DiyunZ/printer-energy-monitor-wiring/connector_detail.png

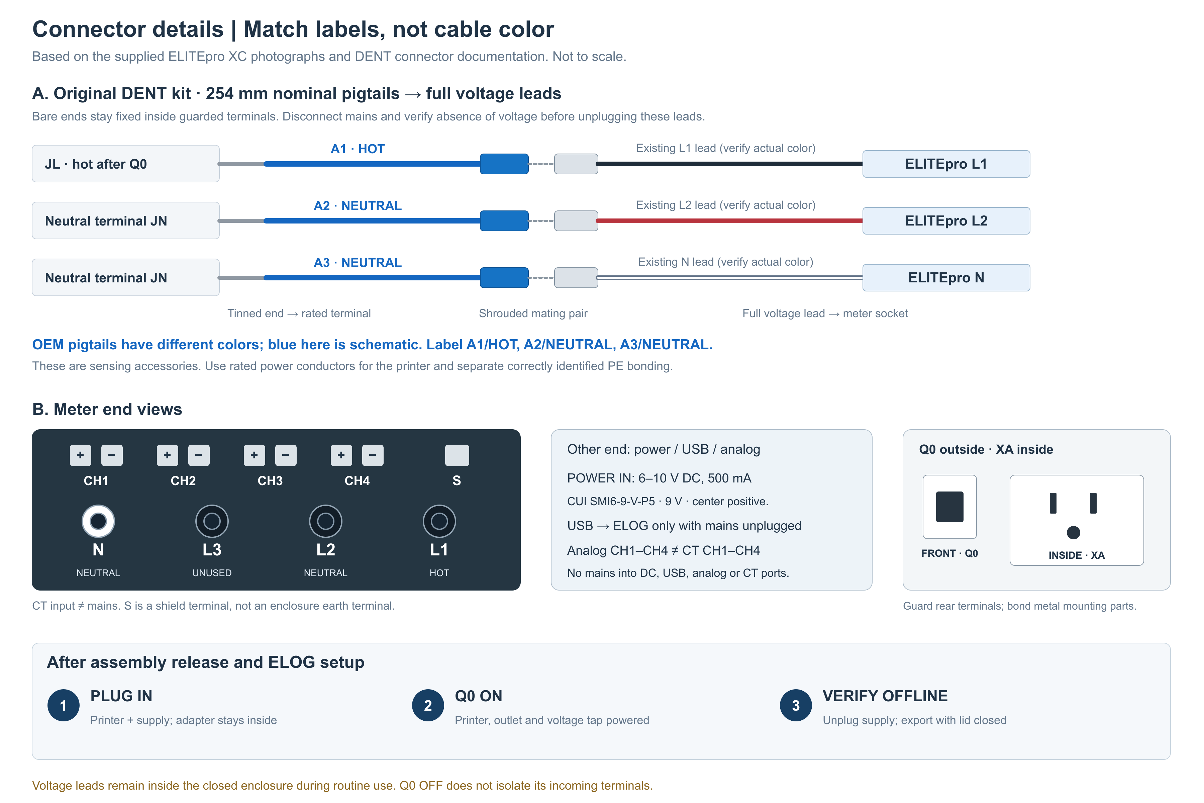
connector_detail.png
