DiyunZ/printer-energy-monitor-wiring/assets/materials/breaker.jpg

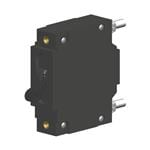
assets/materials/breaker.jpg
