DiyunZ/printer-energy-monitor-wiring/assets/materials/cord-glands.jpg

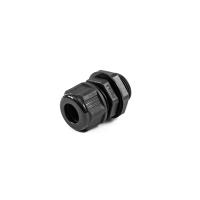
assets/materials/cord-glands.jpg
