DiyunZ/printer-energy-monitor-wiring/assets/materials/enclosure-nbf32126.jpg

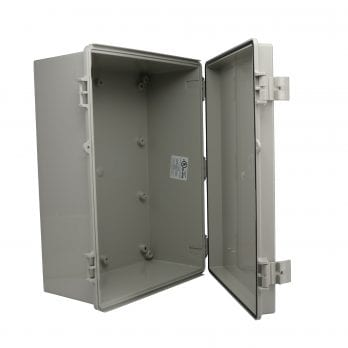
assets/materials/enclosure-nbf32126.jpg
