DiyunZ/printer-energy-monitor-wiring/assets/materials/fasteners-photo.jpg

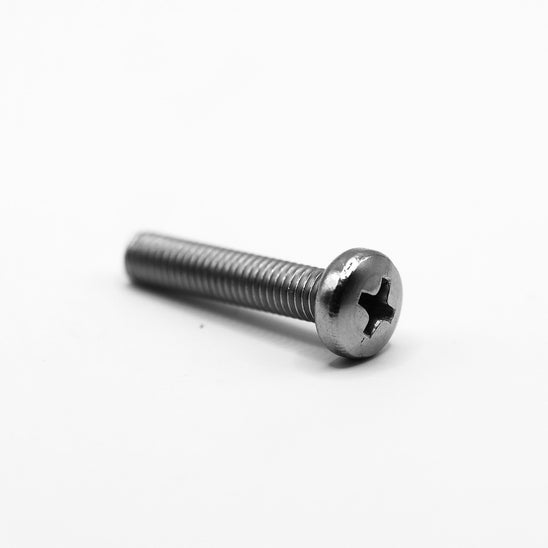
assets/materials/fasteners-photo.jpg
