DiyunZ/printer-energy-monitor-wiring/assets/materials/request-36-4703-ND.jpg

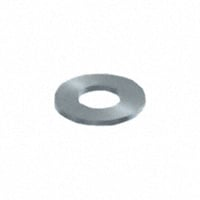
assets/materials/request-36-4703-ND.jpg
