DiyunZ/printer-energy-monitor-wiring/assets/materials/request-36-4705-ND.jpg

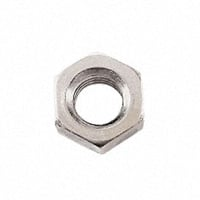
assets/materials/request-36-4705-ND.jpg
