DiyunZ/printer-energy-monitor-wiring/assets/materials/request-36-9911-ND.jpg

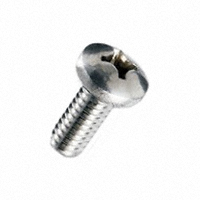
assets/materials/request-36-9911-ND.jpg
