DiyunZ/printer-energy-monitor-wiring/assets/materials/request-277-11849-ND.jpg

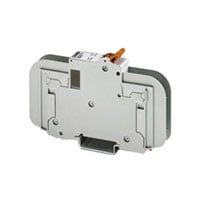
assets/materials/request-277-11849-ND.jpg
