DiyunZ/printer-energy-monitor-wiring/assets/materials/request-298-1030-ND.jpg

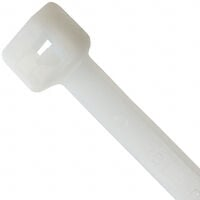
assets/materials/request-298-1030-ND.jpg
