DiyunZ/printer-energy-monitor-wiring/assets/materials/request-298-10245-ND.jpg

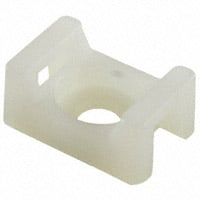
assets/materials/request-298-10245-ND.jpg
