DiyunZ/printer-energy-monitor-wiring/assets/materials/request-3720-3104-ND.jpg

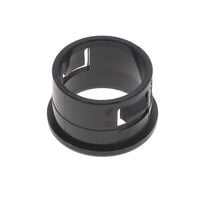
assets/materials/request-3720-3104-ND.jpg
