DiyunZ/printer-energy-monitor-wiring/assets/materials/request-204801237.jpg

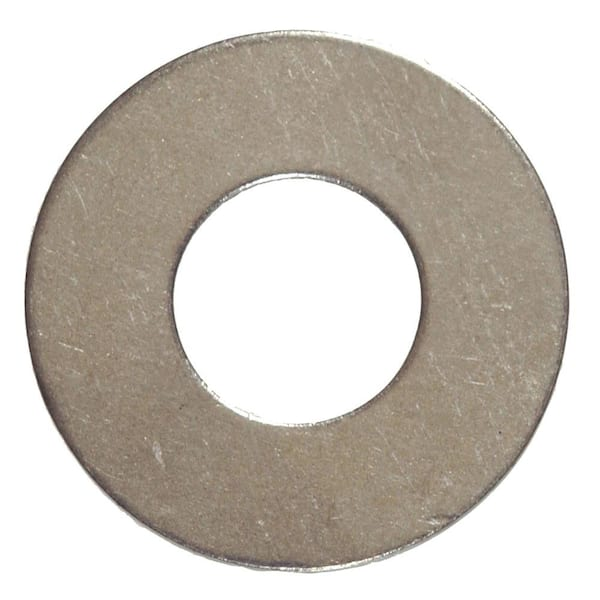
assets/materials/request-204801237.jpg
