DiyunZ/printer-energy-monitor-wiring/assets/materials/request-301304939.jpg

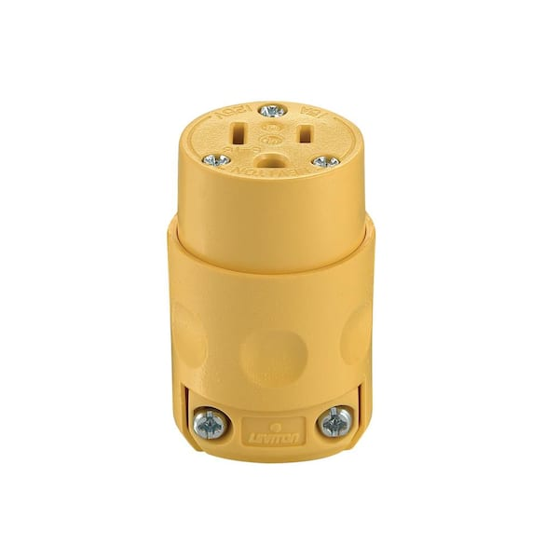
assets/materials/request-301304939.jpg
