DiyunZ/printer-energy-monitor-wiring/assets/materials/request-309610976.jpg

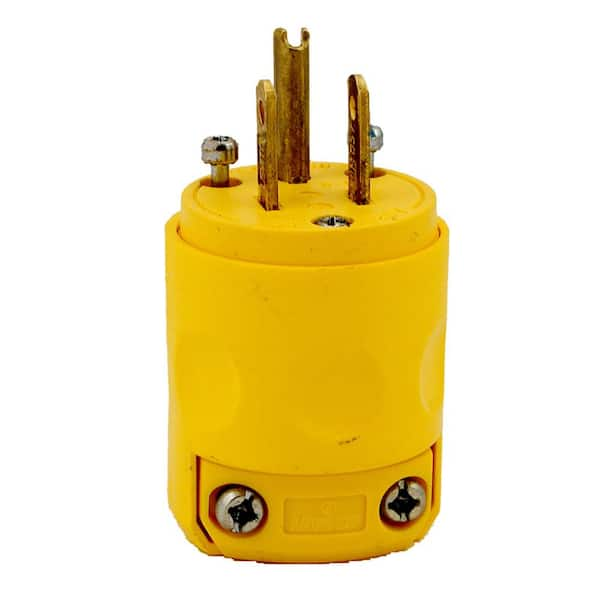
assets/materials/request-309610976.jpg
