DiyunZ/printer-energy-monitor-wiring/assets/materials/request-317479556.jpg

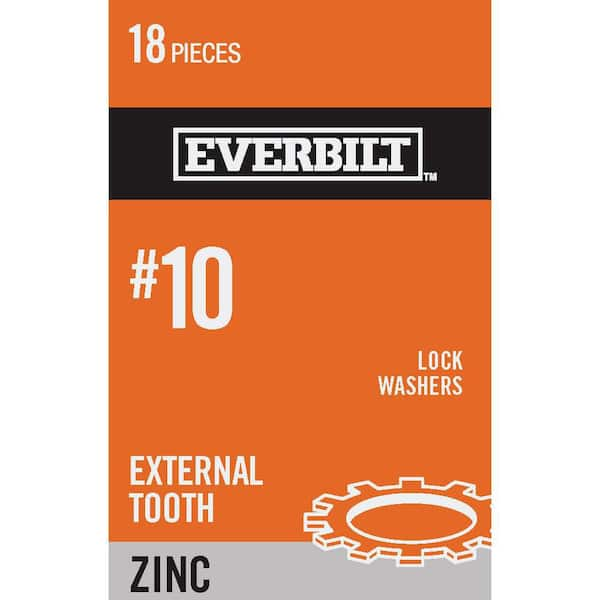
assets/materials/request-317479556.jpg
