DiyunZ/printer-energy-monitor-wiring/assets/materials/request-321071623.jpg

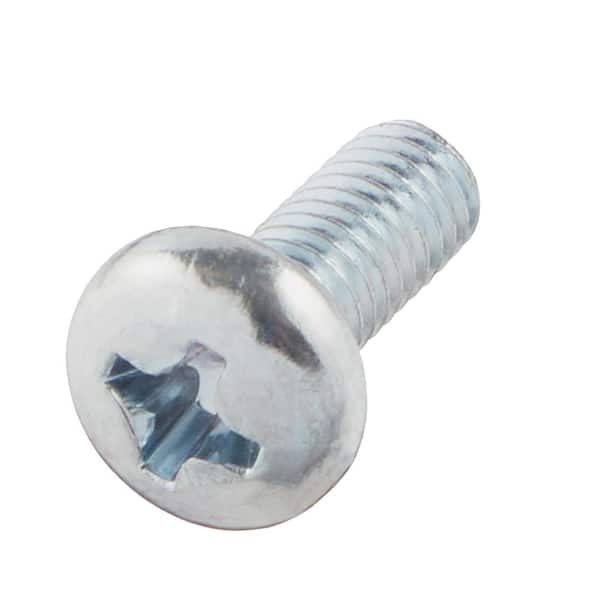
assets/materials/request-321071623.jpg
