DiyunZ/printer-energy-monitor-wiring/assets/materials/request-321071719.jpg

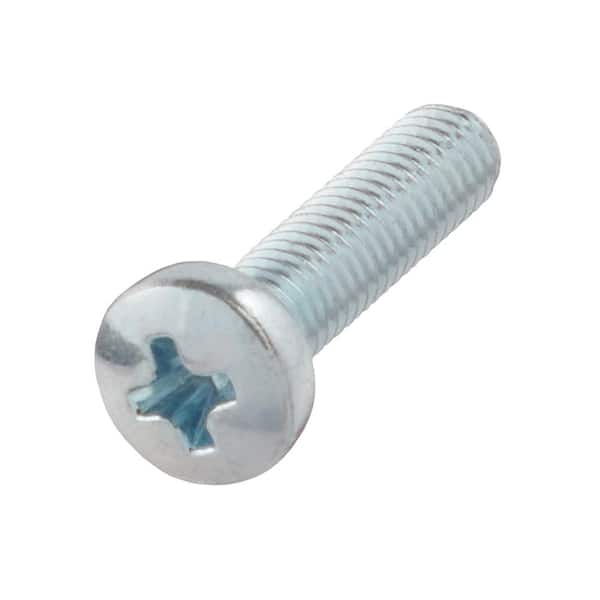
assets/materials/request-321071719.jpg
