DiyunZ/printer-energy-monitor-wiring/assets/materials/request-323370995.jpg

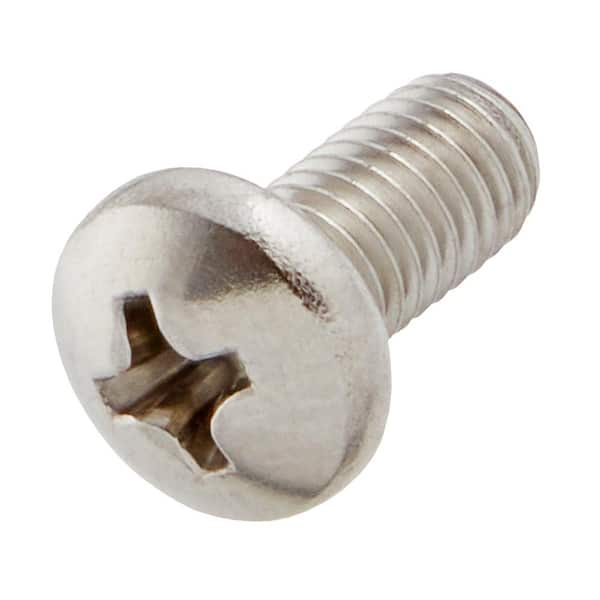
assets/materials/request-323370995.jpg
