DiyunZ/printer-energy-monitor-wiring/wiring_routes.png

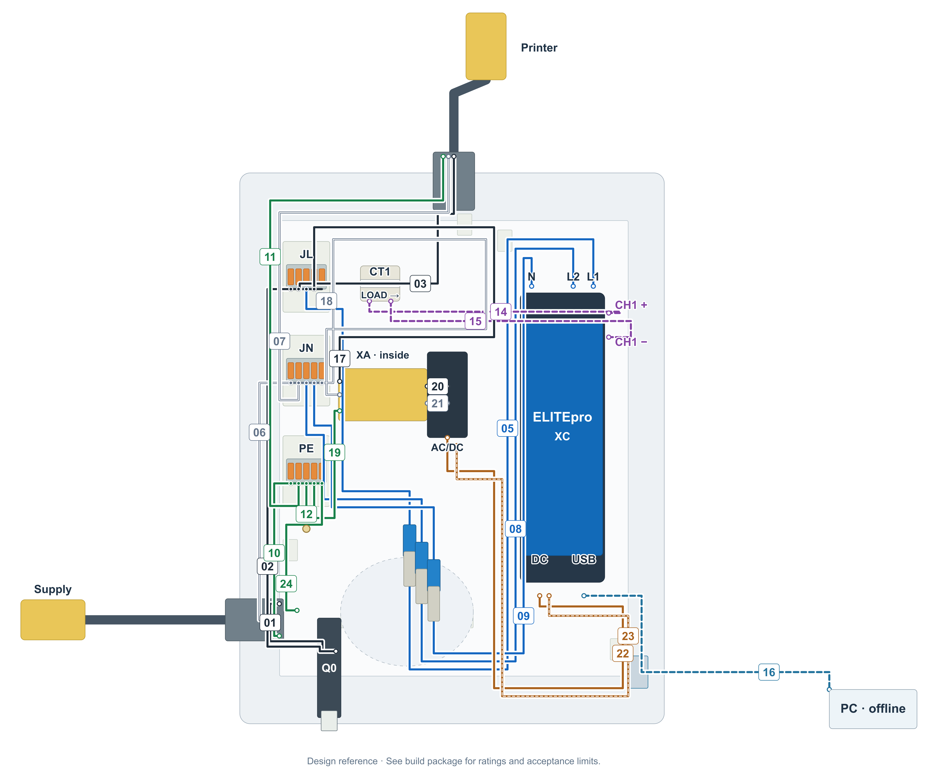
wiring_routes.png
