DiyunZ/printer-energy-monitor-wiring/assets/materials/meter.jpg

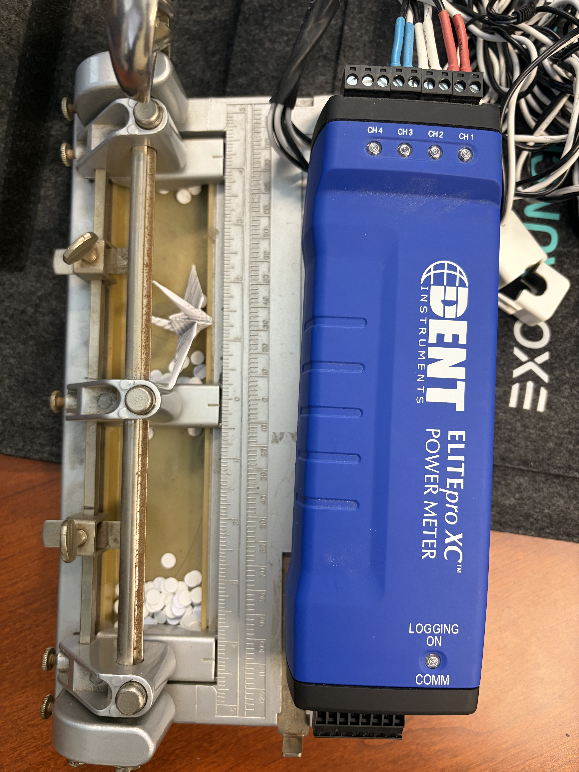
[picture p24: assets/materials/meter.jpg]
assets/materials/meter.jpg
