DiyunZ/printer-energy-monitor-wiring/assets/materials/voltage-leads.jpg

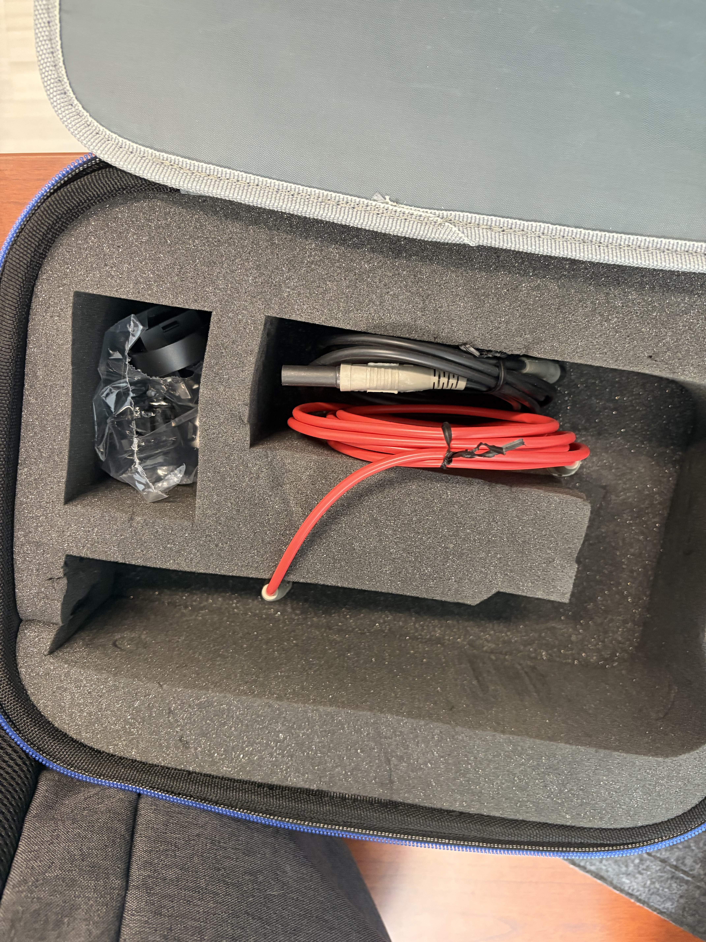
[picture p27: assets/materials/voltage-leads.jpg]
assets/materials/voltage-leads.jpg
