DiyunZ/printer-energy-monitor-wiring/assets/materials/adapter.jpg

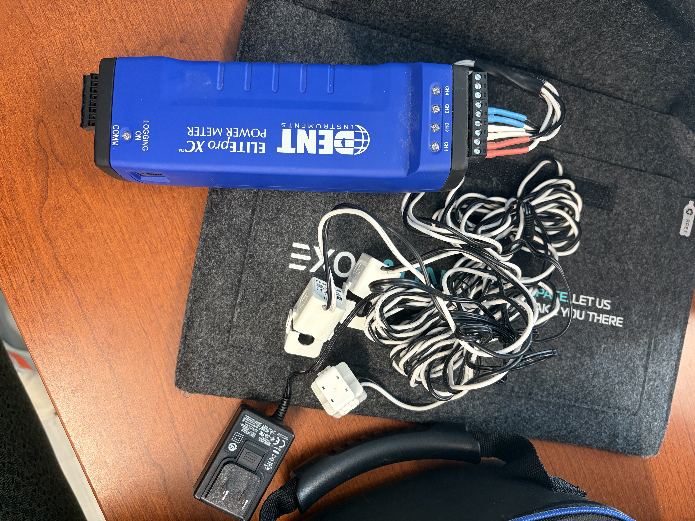
[picture p28: assets/materials/adapter.jpg]
assets/materials/adapter.jpg
